kastoria2/LedNetworkCabinet/firmware/src/HexPanel.cpp

#include "HexPanel.h"

HexPanel::HexPanel(int width_mm, int height_mm) : width_mm(width_mm), height_mm(height_mm),
    ledStrip {
        LedOut {0, {75.0,86.602}, NeoPixels::Color(0,0,0)},
        LedOut {1, {174.999,86.602}, NeoPixels::Color(0,0,0)},
        LedOut {2, {225.0,86.602}, NeoPixels::Color(0,0,0)},
        LedOut {3, {325.0,86.602}, NeoPixels::Color(0,0,0)},
        LedOut {4, {375.0,86.602}, NeoPixels::Color(0,0,0)},
        LedOut {5, {475.0,86.602}, NeoPixels::Color(0,0,0)},
        LedOut {6, {525.0,86.602}, NeoPixels::Color(0,0,0)},
        LedOut {7, {550.0,129.903}, NeoPixels::Color(0,0,0)},
        LedOut {8, {450.0,129.903}, NeoPixels::Color(0,0,0)},
        LedOut {9, {400.0,129.903}, NeoPixels::Color(0,0,0)},
        LedOut {10, {300.0,129.903}, NeoPixels::Color(0,0,0)},
        LedOut {11, {249.999,129.903}, NeoPixels::Color(0,0,0)},
        LedOut {12, {150.0,129.903}, NeoPixels::Color(0,0,0)},
        LedOut {13, {99.999,129.903}, NeoPixels::Color(0,0,0)},
        LedOut {14, {75.0,173.205}, NeoPixels::Color(0,0,0)},
        LedOut {15, {174.999,173.205}, NeoPixels::Color(0,0,0)},
        LedOut {16, {225.0,173.205}, NeoPixels::Color(0,0,0)},
        LedOut {17, {325.0,173.205}, NeoPixels::Color(0,0,0)},
        LedOut {18, {375.0,173.205}, NeoPixels::Color(0,0,0)},
        LedOut {19, {475.0,173.205}, NeoPixels::Color(0,0,0)},
        LedOut {20, {525.0,173.205}, NeoPixels::Color(0,0,0)},
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
        LedOut {88, {375.0,606.217}, NeoPixels::Color(0,0,0)},
        LedOut {89, {475.0,606.217}, NeoPixels::Color(0,0,0)},
        LedOut {90, {525.0,606.217}, NeoPixels::Color(0,0,0)},
        LedOut {91, {550.0,649.519}, NeoPixels::Color(0,0,0)},
        LedOut {92, {450.0,649.519}, NeoPixels::Color(0,0,0)},
        LedOut {93, {400.0,649.519}, NeoPixels::Color(0,0,0)},
        LedOut {94, {300.0,649.519}, NeoPixels::Color(0,0,0)},
        LedOut {95, {249.999,649.519}, NeoPixels::Color(0,0,0)},
        LedOut {96, {150.0,649.519}, NeoPixels::Color(0,0,0)},
        LedOut {97, {99.999,649.519}, NeoPixels::Color(0,0,0)}
    }
{}

LedOut* HexPanel::getLedStrip()
{
    return this->ledStrip;
}

int HexPanel::getLedCount()
{
    return NUM_LEDS;
}
